kylemath/CableRack/print/print_insert_power_plug.3mf

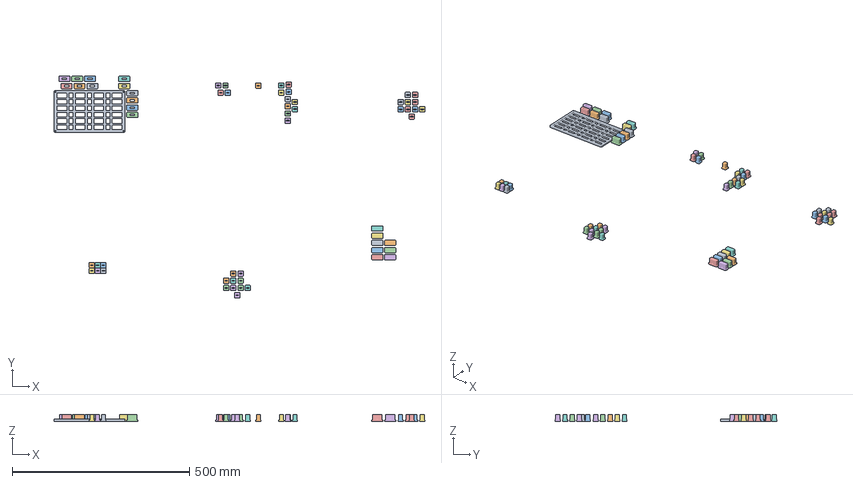
[picture p16: CAD file, 2026-05-14]
print/print_insert_power_plug.3mf
1045.3 x 624.9 x 19.0 mm
print_frame_mixed_7x6mixed.stl
print_insert_lightning_narrow.stl x 11
print_insert_micro_narrow.stl x 15
print_insert_usbc_narrow.stl x 15
print_insert_usba.stl x 12
print_insert_blank.stl x 8
