kylemath/CableRack/print/print_frame_mixed_3n_3rows.stl

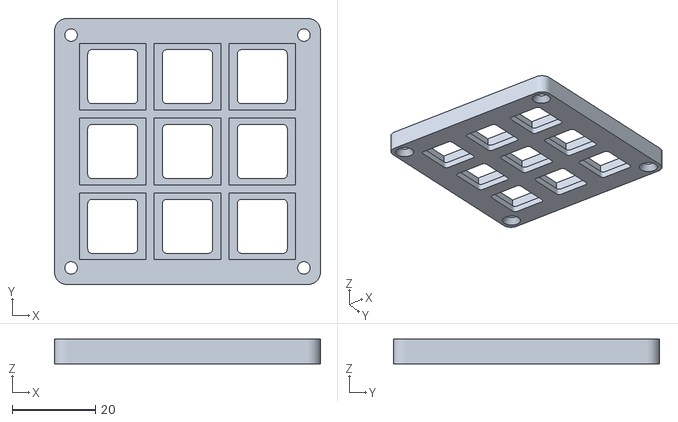
[picture p17: CAD file, 2026-05-14]
print/print_frame_mixed_3n_3rows.stl
64.0 x 64.0 x 6.00
