kylemath/CableRack/print/print_frame_mixed_4n_2rows.stl

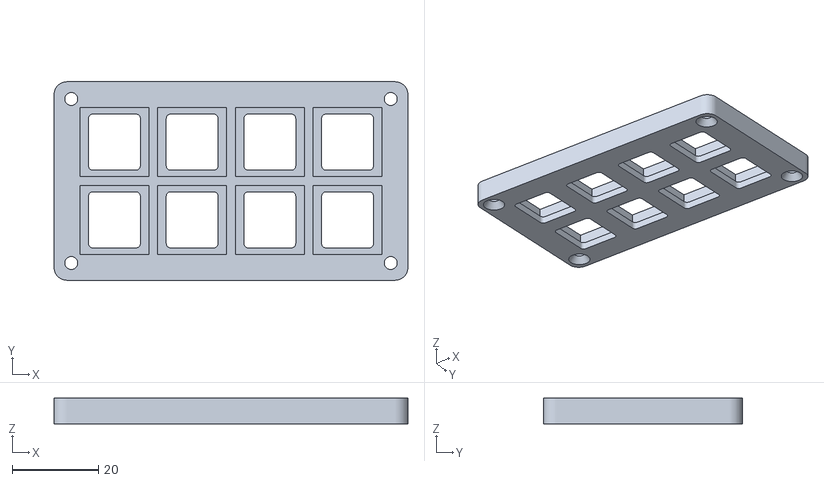
[picture p18: CAD file, 2026-05-14]
print/print_frame_mixed_4n_2rows.stl
82.0 x 46.0 x 6.00
