kylemath/CableRack/print/print_insert_blank_narrow.stl

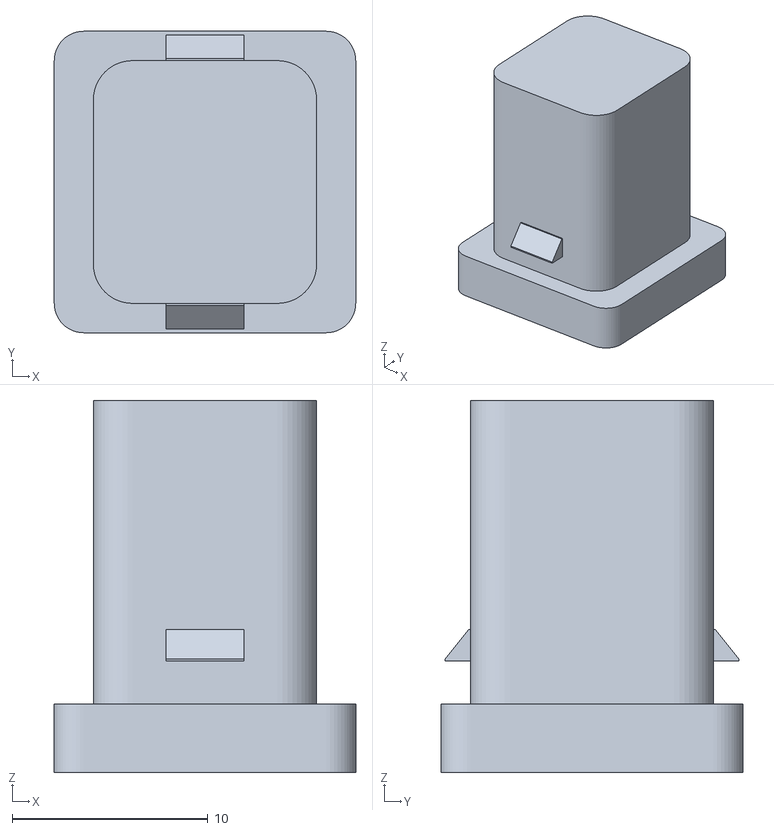
[picture p19: CAD file, 2026-05-14]
print/print_insert_blank_narrow.stl
15.4 x 15.4 x 19.0
