kylemath/CableRack/print/print_frame_3x3.stl

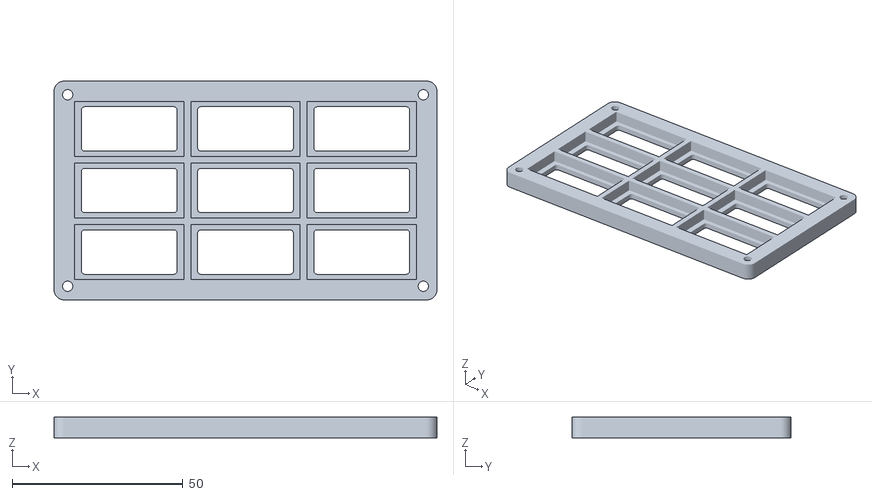
[picture p20: CAD file, 2026-05-14]
print/print_frame_3x3.stl
112.0 x 64.0 x 6.00
