kylemath/CableRack/insert_audio_jack.scad

// ============================================
// 3.5MM AUDIO JACK FEMALE INSERT
// Port: Ø6.0mm circular
// ============================================

include <insert_base.scad>

module insert_audio_jack() {
    insert_with_port() port_audio_jack();
}

// Render
insert_audio_jack();
