kylemath/CableRack/insert_lightning.scad

// ============================================
// LIGHTNING FEMALE INSERT
// Port: 6.7mm x 1.5mm rounded rectangle
// ============================================

include <insert_base.scad>

module insert_lightning() {
    insert_with_port() port_lightning();
}

// Render
insert_lightning();
