kylemath/CableRack/insert_usb_b.scad

// ============================================
// USB-B FEMALE INSERT
// Port: 8.0mm x 7.5mm with beveled top corners
// ============================================

include <insert_base.scad>

module insert_usb_b() {
    insert_with_port() port_usb_b();
}

// Render
insert_usb_b();
