kylemath/CableRack/insert_usb_micro.scad

// ============================================
// USB MICRO FEMALE INSERT
// Port: 6.9mm x 1.8mm rounded rectangle
// ============================================

include <insert_base.scad>

module insert_usb_micro() {
    insert_with_port() port_usb_micro();
}

// Render
insert_usb_micro();
