kylemath/CableRack/insert_usb_mini.scad

// ============================================
// USB MINI FEMALE INSERT
// Port: 6.9mm x 3.0mm rounded rectangle
// ============================================

include <insert_base.scad>

module insert_usb_mini() {
    insert_with_port() port_usb_mini();
}

// Render
insert_usb_mini();
