kylemath/CableRack/insert_usba.scad

// ============================================
// USB-A FEMALE INSERT
// Port: 14.0mm x 6.5mm rectangle
// ============================================

include <insert_base.scad>

module insert_usba() {
    insert_with_port() port_usba();
}

// Render
insert_usba();
