kylemath/CableRack/print_frame_4x4.scad

// ============================================
// PRINT FILE: 4x4 Frame (16 slots)
// ============================================
// Print with back side down (no supports needed)
// Frame size: ~145mm x 80.5mm
// ============================================

include <frame_module.scad>

// Render 4x4 frame (16 slots)
grid_frame(cols=4, rows=4);
