kylemath/CableRack/print_frame_6x6.scad

// ============================================
// PRINT FILE: 6x6 Frame (36 slots)
// ============================================
// Print with back side down (no supports needed)
// Frame size: ~209mm x 112.5mm
// ============================================

include <frame_module.scad>

// Render 6x6 frame (36 slots)
grid_frame(cols=6, rows=6);
