kylemath/CableRack/print_frame_mixed_2n2w_2rows.scad

// ============================================
// PRINT FILE: Mixed Frame - 2 Narrow + 2 Wide (2 rows)
// ============================================
// 4 columns x 2 rows = 8 slots
// Columns: Narrow, Narrow, Wide, Wide
// Balanced configuration for common and larger connectors
// Print with back side down (no supports needed)
// ============================================

include <frame_variable.scad>

// Column widths: N=narrow (16mm), W=wide (32mm)
col_widths = [N, N, W, W];
rows = 2;

// Render
grid_frame_variable(col_widths, rows);
