kylemath/CableRack/print_frame_single.scad

// ============================================
// PRINT FILE: Single Slot Frame (1x1)
// ============================================
// Print with back side down (no supports needed)
// Frame size: ~48.5mm x 32.5mm
// ============================================

include <frame_module.scad>

// Render 1x1 frame (1 slot)
grid_frame(cols=1, rows=1);
