kylemath/CableRack/print_insert_audio_jack_narrow.scad

// ============================================
// PRINT FILE: 3.5mm Audio Jack Insert (NARROW)
// ============================================
// Narrow width version for space-efficient frames
// Print with base down (no supports needed)
// ============================================

include <insert_base.scad>

// Render narrow Audio Jack insert
insert_audio_jack_narrow();
