kylemath/CableRack/print_insert_blank_label_narrow.scad

// ============================================
// PRINT FILE: Blank Label Insert (NARROW)
// ============================================
// Narrow width version with recessed area for labels
// Print with base down (no supports needed)
// Use for custom labels or text (paint, sticker, etc.)
// ============================================

include <insert_base.scad>

// Render narrow blank label insert
insert_blank_label_narrow();
