kylemath/CableRack/print_insert_blank_narrow.scad

// ============================================
// PRINT FILE: Blank Insert (NARROW)
// ============================================
// Narrow width version for space-efficient frames
// Use to fill unused slots or for custom modifications
// Print with base down (no supports needed)
// ============================================

include <insert_base.scad>

// Render narrow blank insert
insert_blank_narrow();
