kylemath/CableRack/print_insert_power_plug.scad

// ============================================
// PRINT FILE: AC Power Plug Insert (2-prong)
// ============================================
// US-style 2-prong power plug with asymmetric holes
// Hot (narrow) and Neutral (wide) prongs for polarity
// NO GROUND HOLE - use blank insert below for ground pin
// Print with base down (no supports needed)
// ============================================

include <insert_base.scad>

// Render power plug insert
insert_power_plug();
