kylemath/CableRack/print_insert_universal_displayport.scad

// ============================================
// PRINT FILE: Universal DisplayPort Adapter Insert
// ============================================
// Accepts DisplayPort male connector on front
// Routes to 24-pin universal interface on rear
// Native routing - no active conversion needed
// ============================================

include <insert_universal_base.scad>

// Render the universal DisplayPort adapter
insert_universal_displayport();
