kylemath/CableRack/print_insert_universal_hdmi.scad

// ============================================
// PRINT FILE: Universal HDMI Adapter Insert
// ============================================
// Accepts HDMI male connector on front
// Routes to 24-pin universal interface on rear
// NOTE: Requires active TMDS-to-DP converter IC
// ============================================

include <insert_universal_base.scad>

// Render the universal HDMI adapter
insert_universal_hdmi();
