kylemath/CableRack/print_insert_universal_usbc.scad

// ============================================
// PRINT FILE: Universal USB-C Adapter Insert
// ============================================
// Accepts USB-C male connector on front
// Routes to 24-pin universal interface on rear
// ============================================

include <insert_universal_base.scad>

// Render the universal USB-C adapter
insert_universal_usbc();
