kylemath/CableRack/print_insert_usb_b.scad

// ============================================
// PRINT FILE: USB-B Insert
// ============================================
// Body depth: 14mm (matches USB-B male connector)
// Print with port side DOWN (flat on bed)
// No supports needed - through-hole design
// ============================================

include <parameters.scad>
include <insert_base.scad>

// USB-B insert - oriented for printing (port side down)
total_depth = insert_base_depth + usb_b_body_depth;

rotate([180, 0, 0])
translate([0, 0, -total_depth])
    insert_usb_b();
