kylemath/CableRack/print_insert_usb_b_narrow.scad

// ============================================
// PRINT FILE: USB-B Insert (NARROW)
// ============================================
// Narrow width version for space-efficient frames
// USB-B is the square connector for printers/keyboards
// Print with base down (no supports needed)
// ============================================

include <insert_base.scad>

// Render narrow USB-B insert
insert_usb_b_narrow();
