kylemath/CableRack/print_universal_male_terminator.scad

// ============================================
// PRINT FILE: Universal Male Terminator
// ============================================
// Cable-end connector that plugs into universal inserts
// Replaces proprietary cable ends with standardized 24-pin plug
// ============================================

include <insert_universal_base.scad>

// Render the universal male terminator
universal_male_terminator();
